mkeveney/Eva3Modifications/evamods_trihorn_beaconmount.jpg

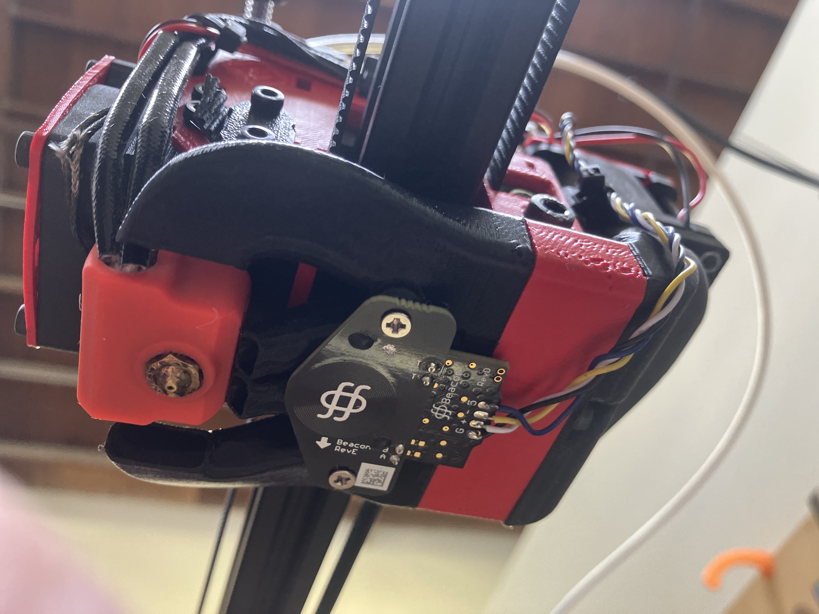
evamods_trihorn_beaconmount.jpg
