mkeveney/Eva3Modifications/evamods_nitehawkmount.jpg

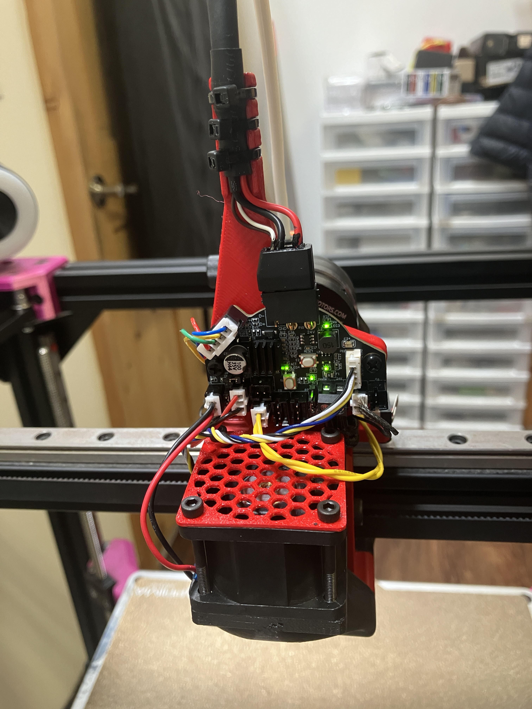
evamods_nitehawkmount.jpg
